wedersonsilva/bioglove/documentation/thesis/figures/arduino-posicao-a.png

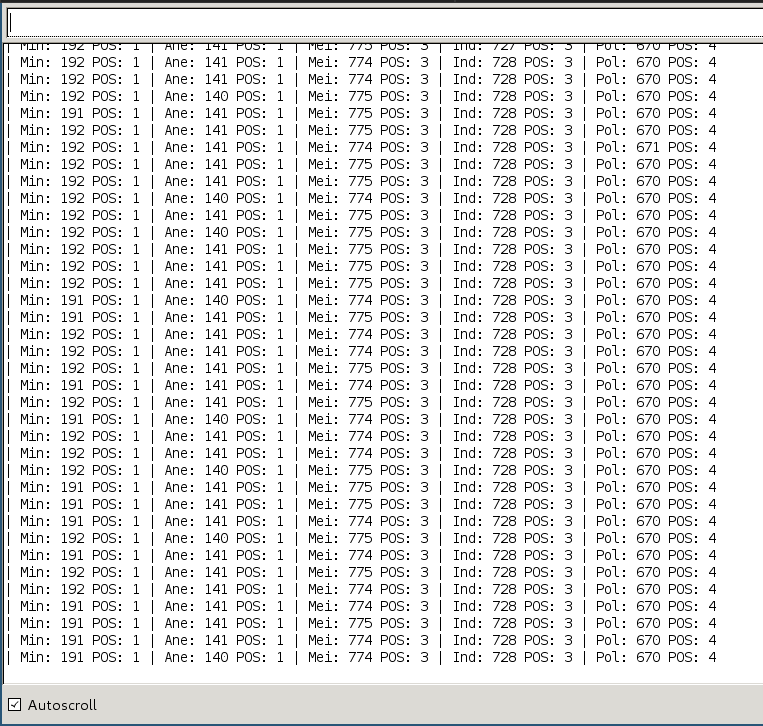
documentation/thesis/figures/arduino-posicao-a.png
