wedersonsilva/bioglove/documentation/thesis/figures/arduino-posicao-b.png

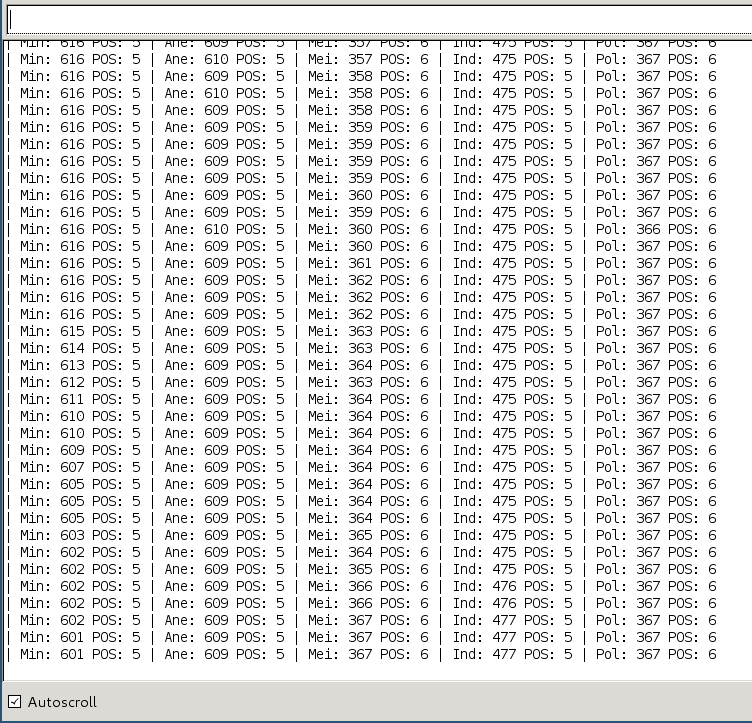
documentation/thesis/figures/arduino-posicao-b.png
