wedersonsilva/bioglove/documentation/thesis/figures/car-black-and-white.png

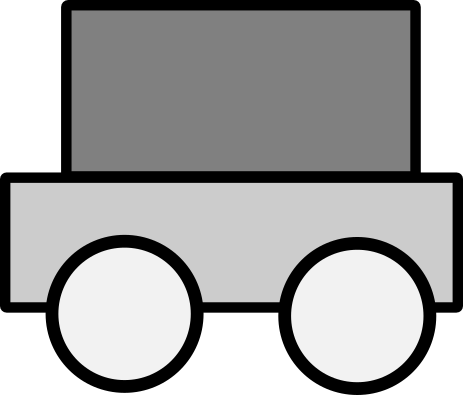
documentation/thesis/figures/car-black-and-white.png
