wedersonsilva/bioglove/documentation/thesis/figures/glove-and-transmitter1.png

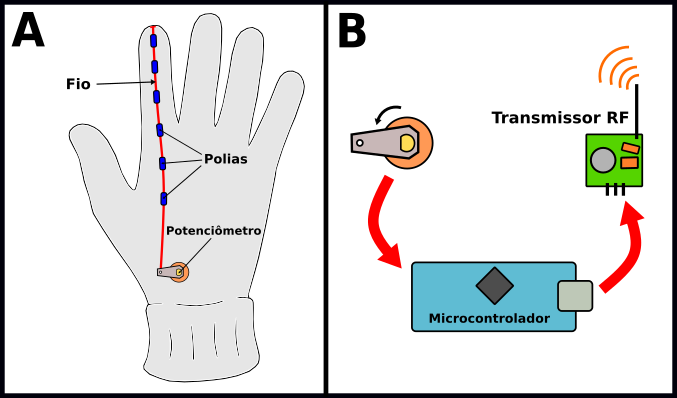
documentation/thesis/figures/glove-and-transmitter1.png
