wedersonsilva/bioglove/documentation/thesis/figures/glove-digital-positions.png

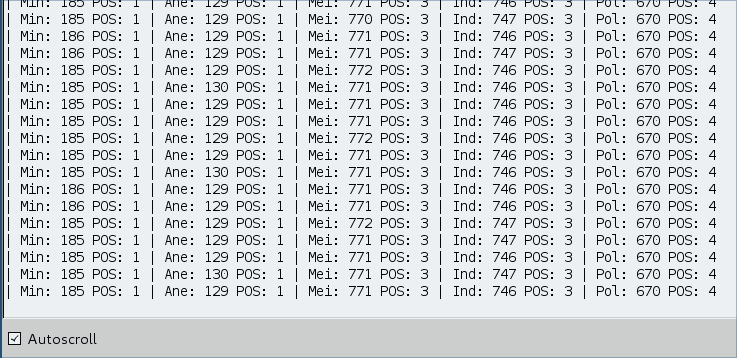
documentation/thesis/figures/glove-digital-positions.png
