wedersonsilva/bioglove/documentation/thesis/figures/glove-finger-number1.png

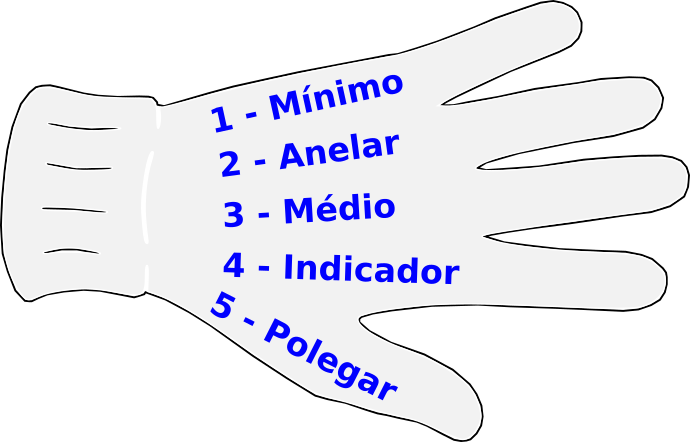
documentation/thesis/figures/glove-finger-number1.png
