wedersonsilva/bioglove/documentation/thesis/figures/glove-positionA.png

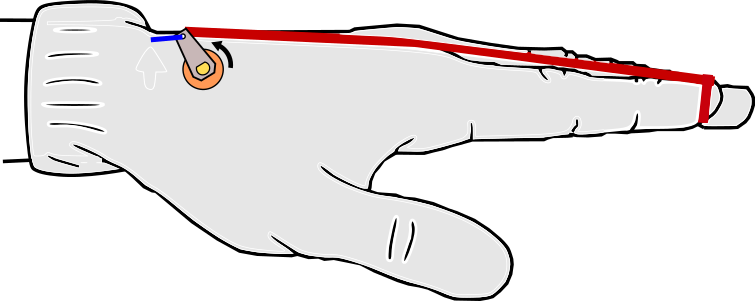
documentation/thesis/figures/glove-positionA.png
