wedersonsilva/bioglove/documentation/thesis/figures/glove-positionB.png

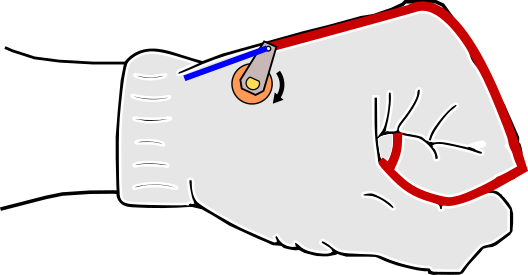
documentation/thesis/figures/glove-positionB.png
