wedersonsilva/bioglove/documentation/thesis/figures/glove-ready-extend2.jpg

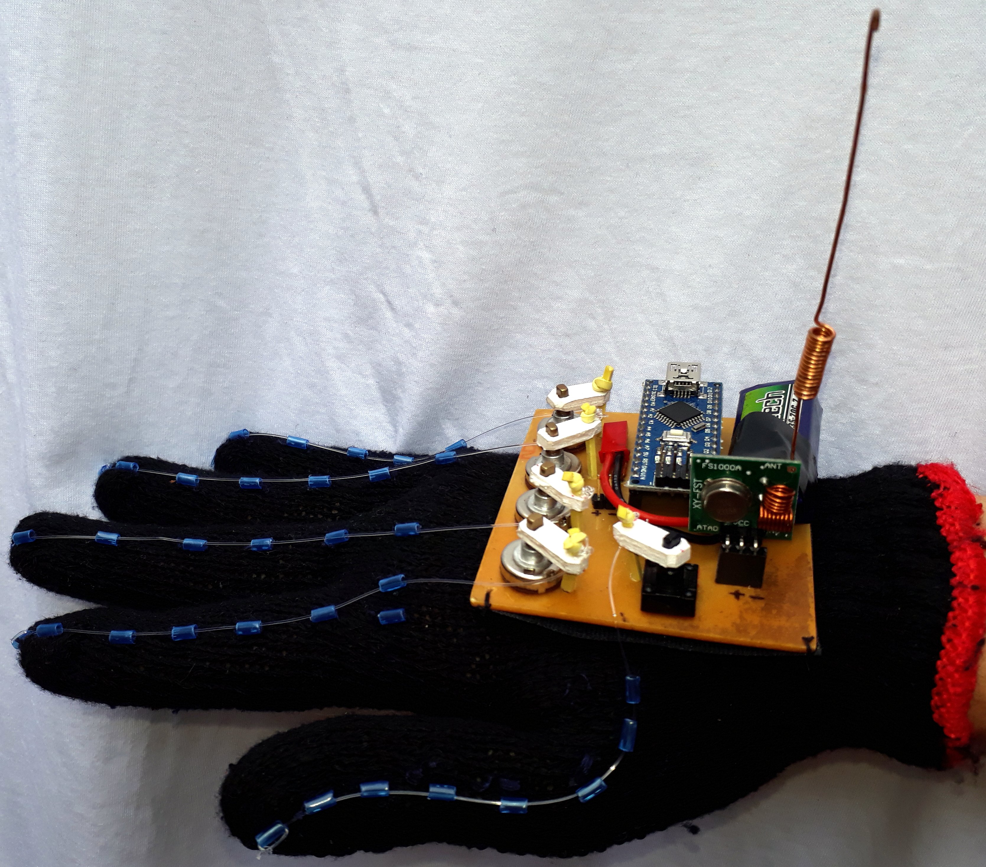
documentation/thesis/figures/glove-ready-extend2.jpg
