wedersonsilva/bioglove/documentation/thesis/figures/glove-ready-flex2.jpg

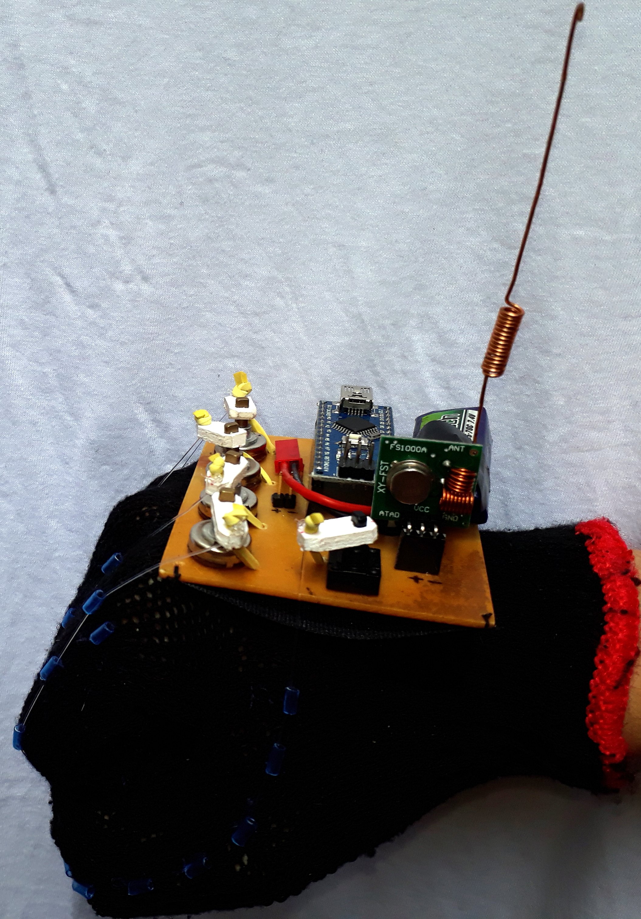
documentation/thesis/figures/glove-ready-flex2.jpg
