wedersonsilva/bioglove/documentation/thesis/figures/receptor-module1.png

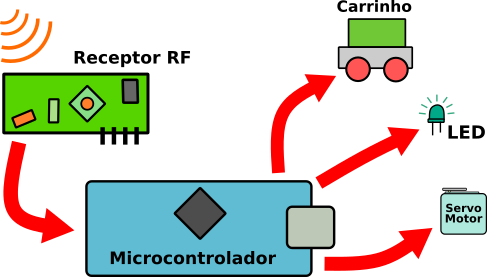
documentation/thesis/figures/receptor-module1.png
