wedersonsilva/bioglove/documentation/thesis/figures/size-glove-module2.png

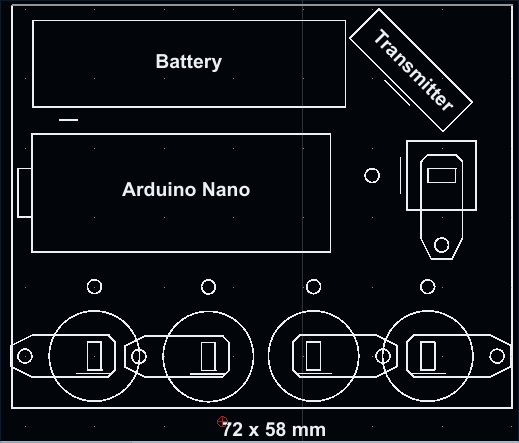
documentation/thesis/figures/size-glove-module2.png
