wedersonsilva/bioglove/documentation/thesis/figures/transmitter-module1.png

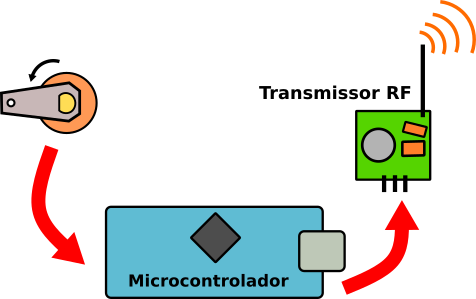
documentation/thesis/figures/transmitter-module1.png
